PR77/rp2040Term/Source/system/system.h

#ifndef SYSTEM_H
#define	SYSTEM_H

#include "pico.h"
#include "pico/stdlib.h"
#include "bsp/board.h"
#include "font.h"

#define LCD_BACKLIGHT_PWM_PIN       28

#if defined (BREADBOARD_PIN_ASSIGNMENTS)
#define LCD_RESET_PON_PIN           26
#else
#define LCD_RESET_PON_PIN           22
#endif

#if defined (BREADBOARD_PIN_ASSIGNMENTS)
#define LCD_HRV_VRV_SCANNING_PIN    22
#else
#define LCD_HRV_VRV_SCANNING_PIN    5
#endif

#define LCD_BACKLIGHTING_PWM_MIN    0
#define LCD_BACKLIGHTING_PWM_MAX    100
#define LCD_BACKLIGHTING_STEP_SIZE  10
#define LCD_BACKLIGHTING_DEFAULT    70

#if defined (BREADBOARD_PIN_ASSIGNMENTS)
#define SOUND_OUTPUT_PIN            27
#else
#define SOUND_OUTPUT_PIN            26
#endif

#define LED_FLASH_INTERVAL_MS       500

#define VIDEO_RENDERING_CORE        1

/* Information on LCD Pixel Clock
.clock_freq = 9500000, // can only be used with set_sys_clock_pll (1482000000, 6, 2) results in a of clock of 123.5MHz;
.clock_freq = 7812500, // can only be used with set_sys_clock_khz (125000, true) results in a of clock of 125.0MHz;
*/

#define LCD_PIXEL_CLK               9500000

typedef struct {
    bool    enableBeeper;
    bool    requestBeeper;
    bool    enableLocalEcho;
    bool    insertLineFeedOnCarriageReturn;
    uint8_t lcdBacklightValue;
} st_systemConfiguration;

extern const scanvideo_mode_t tftLQ042_480x272_60;

void system_initialiseSystem(void);
void system_initialiseAudioPlayer(void);
st_systemConfiguration *system_getSystemConfiguration(void);
void system_toggleBeeper(void);
void system_toggleLocalEcho(void);
void system_toggleCRLF(void);
void system_increaseBacklightByStep(void);
void system_decreaseBacklightByStep(void);
void system_executeSystemReset(void);
void system_onPwmWrap(void);
void system_handleKeyboardAndUartTransmitRouting(char character);
void __time_critical_func(system_renderLoop)(void);
void system_updateLedTask(void);
void system_updateBellTask(void);



#endif // SYSTEM_H
